fabiangeissler/robosax-ledbox/KiCad/output/render top 3d.jpg

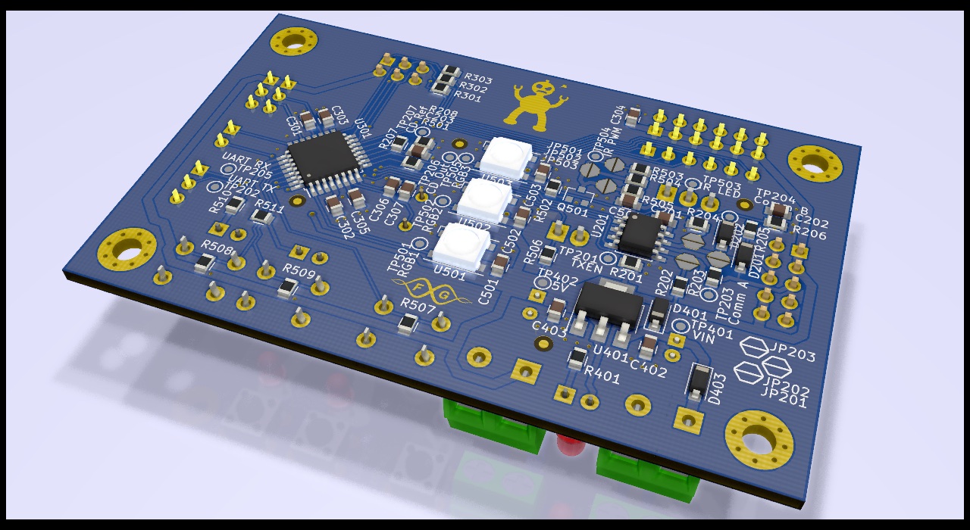
KiCad/output/render top 3d.jpg
