fabiangeissler/robosax-ledbox/Dokumentation/Fotos/IMG_1931.JPG

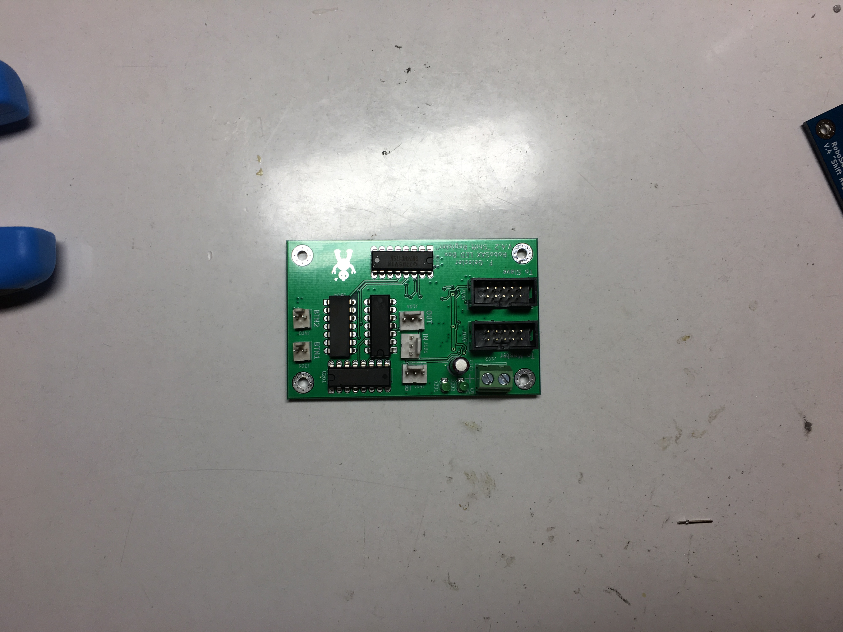
Dokumentation/Fotos/IMG_1931.JPG
