fabiangeissler/robosax-ledbox/Dokumentation/Fotos/IMG_1933.JPG

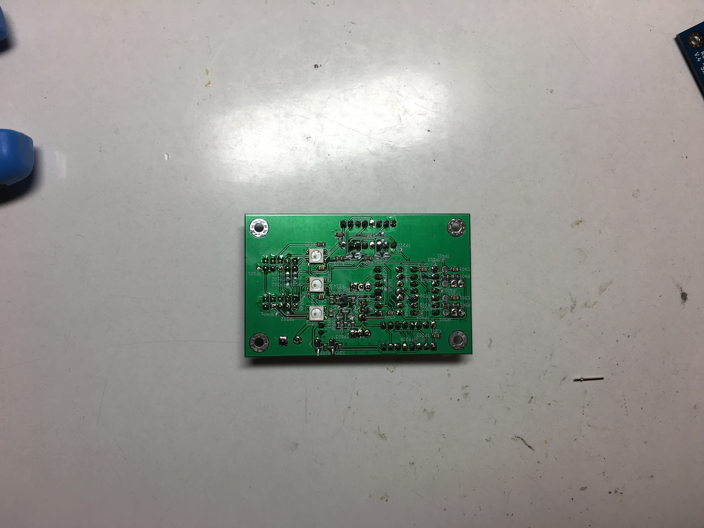
Dokumentation/Fotos/IMG_1933.JPG
