fabiangeissler/robosax-ledbox/Dokumentation/Fotos/IMG_1934.JPG

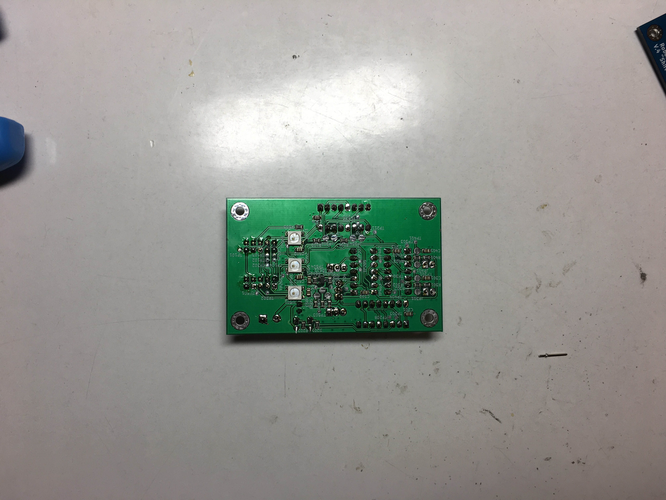
Dokumentation/Fotos/IMG_1934.JPG
