fabiangeissler/robosax-ledbox/Dokumentation/Fotos/IMG_1935.JPG

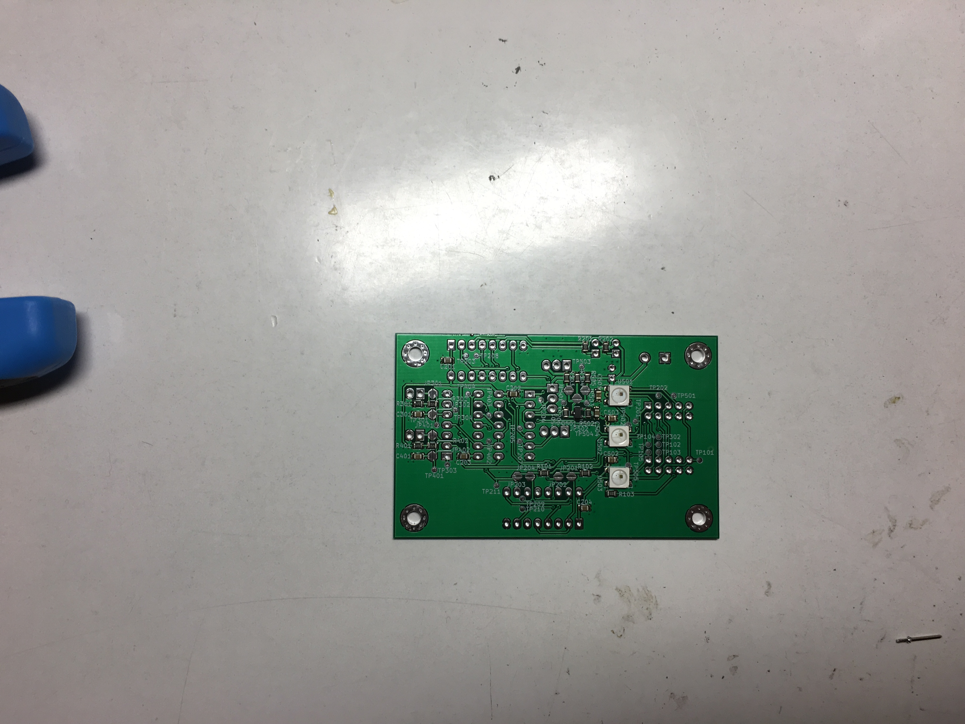
Dokumentation/Fotos/IMG_1935.JPG
