fabiangeissler/robosax-ledbox/KiCad/output/render bot 3d.jpg

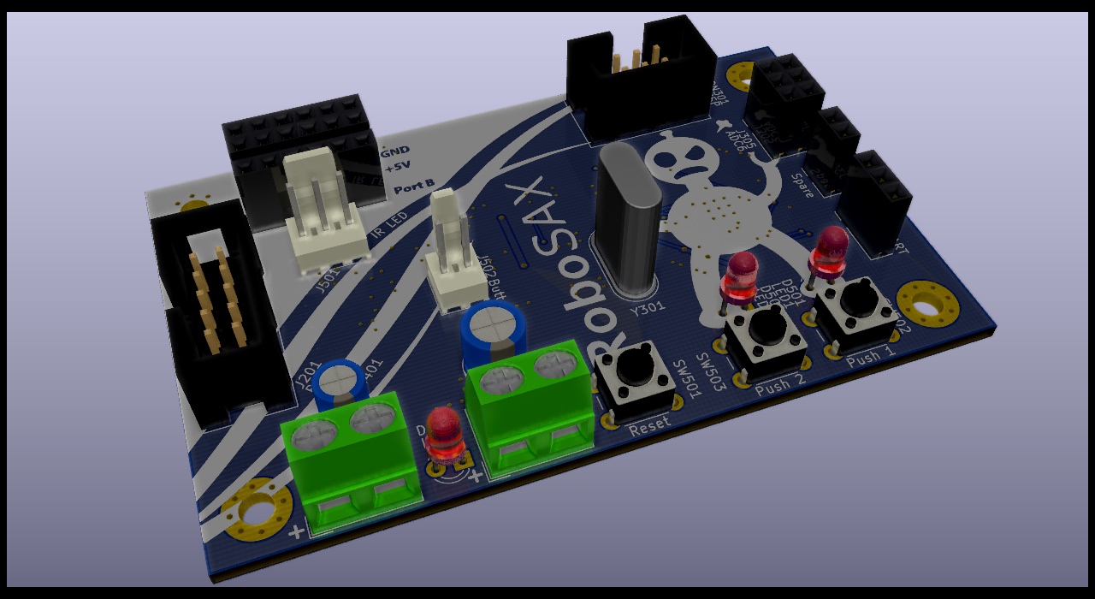
KiCad/output/render bot 3d.jpg
