fabiangeissler/robosax-ledbox/KiCad/output/render bot.jpg

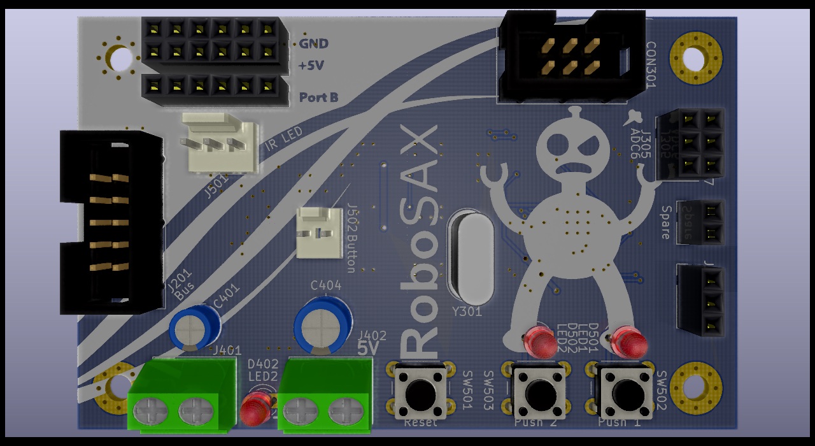
KiCad/output/render bot.jpg
