fabiangeissler/robosax-ledbox/KiCad/output/render top.jpg

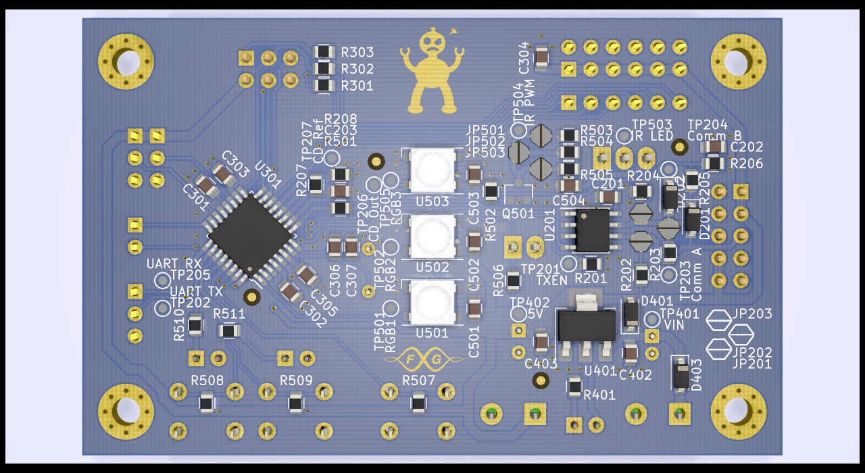
KiCad/output/render top.jpg
