fabiangeissler/robosax-ledbox/KiCad/output/ledbox.pdf

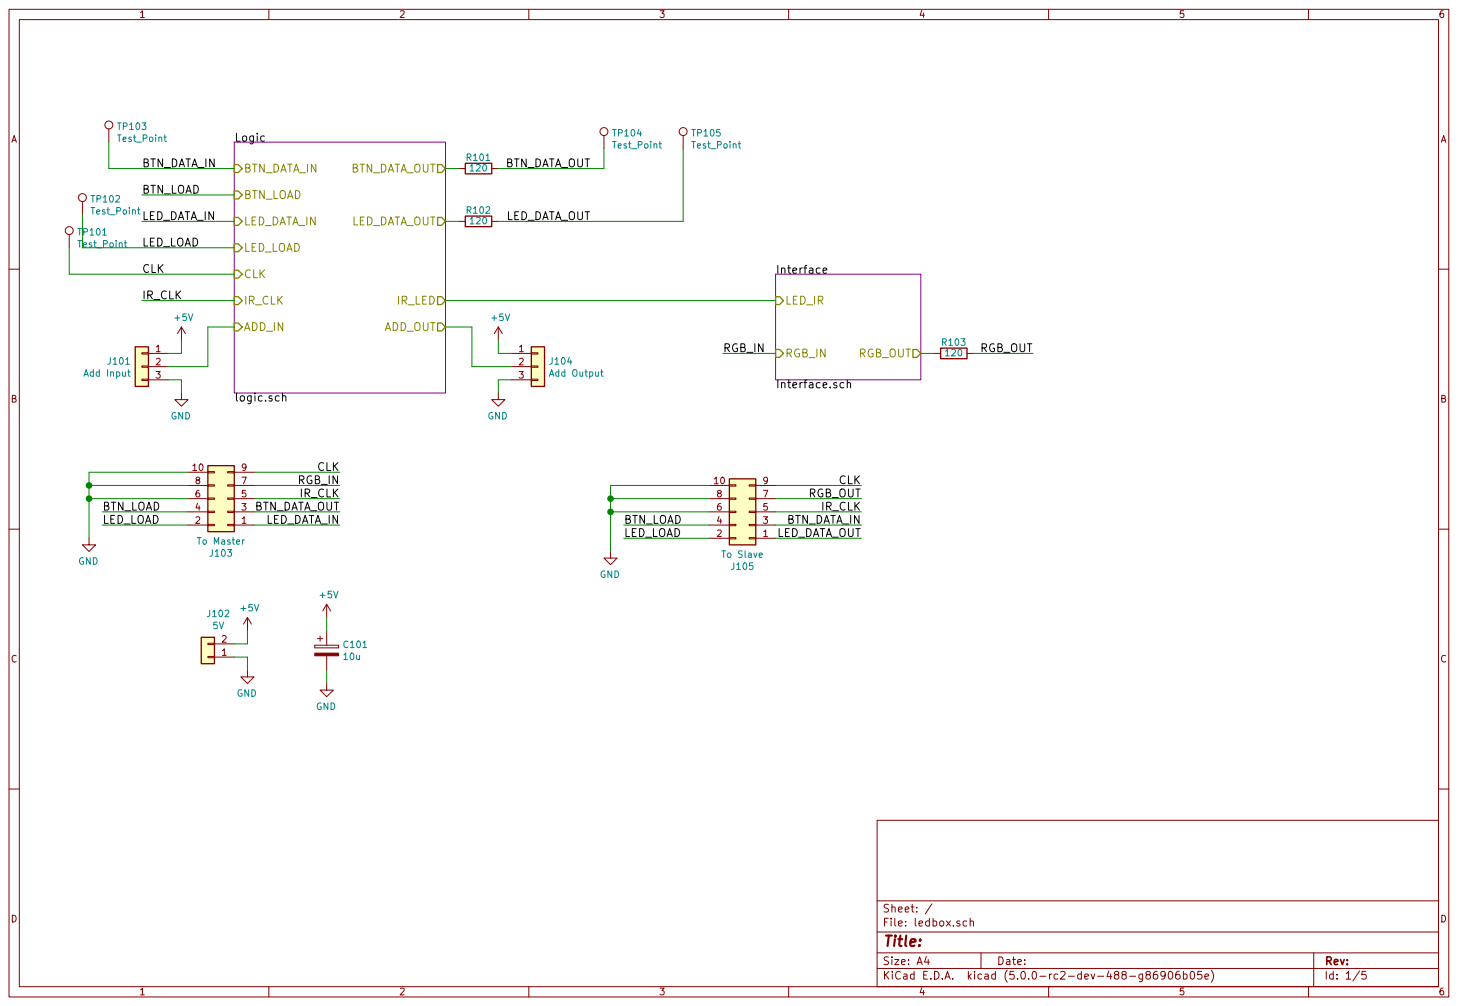
[picture p22: page 1]

Id: 1/5 Title: File: ledbox.sch Sheet: /

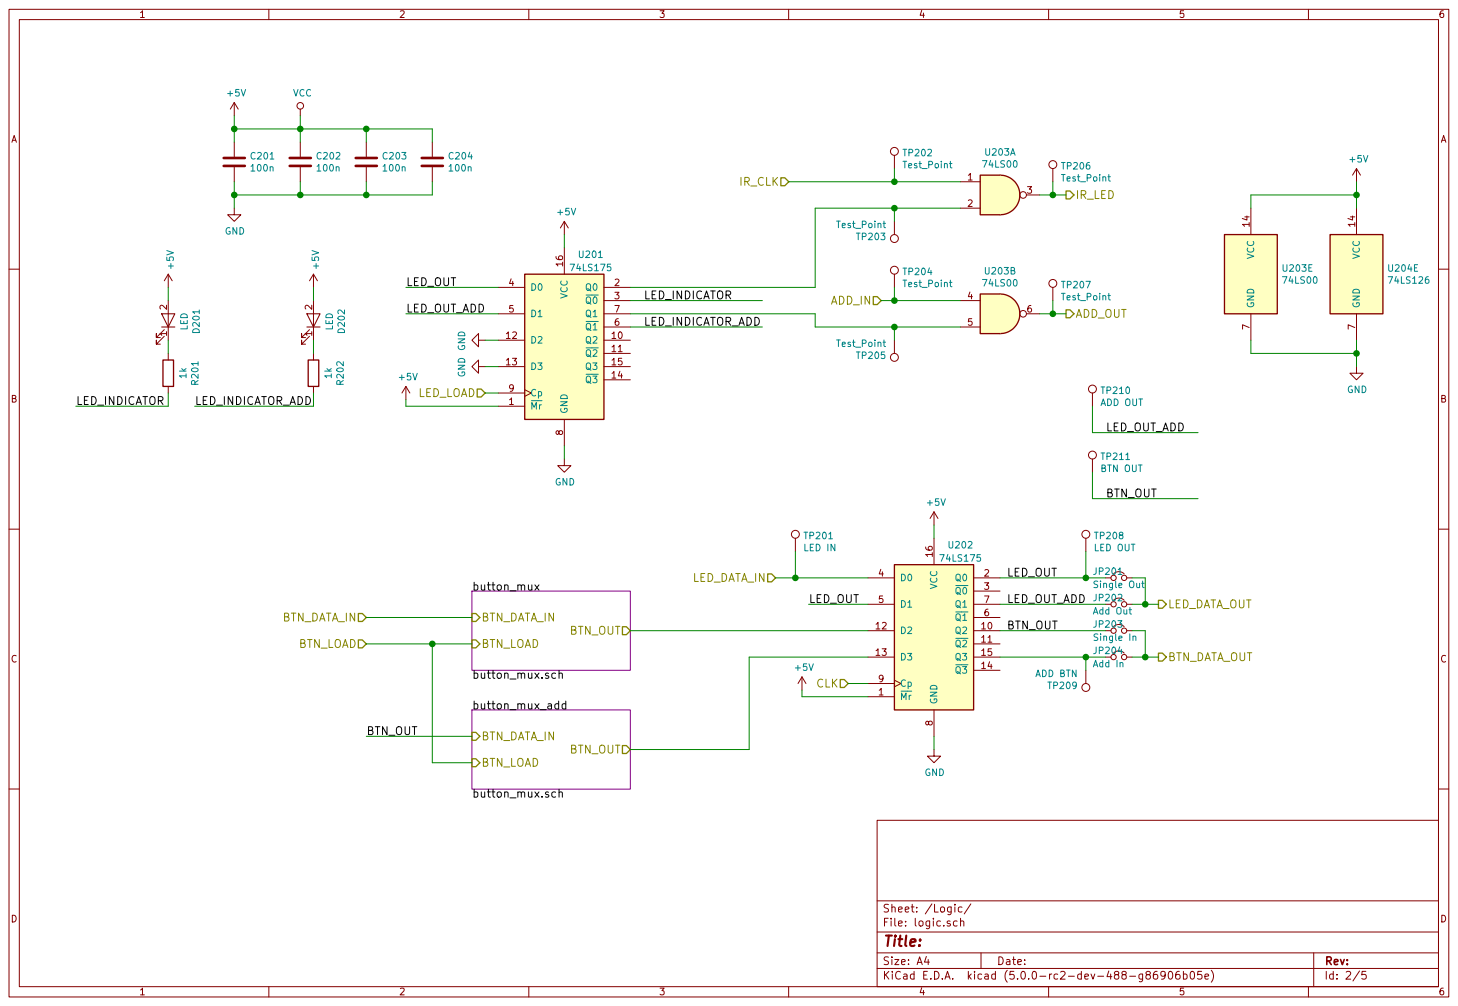
[picture p23: page 2]

JP201 Single Out JP202 Add Out LED_OUT

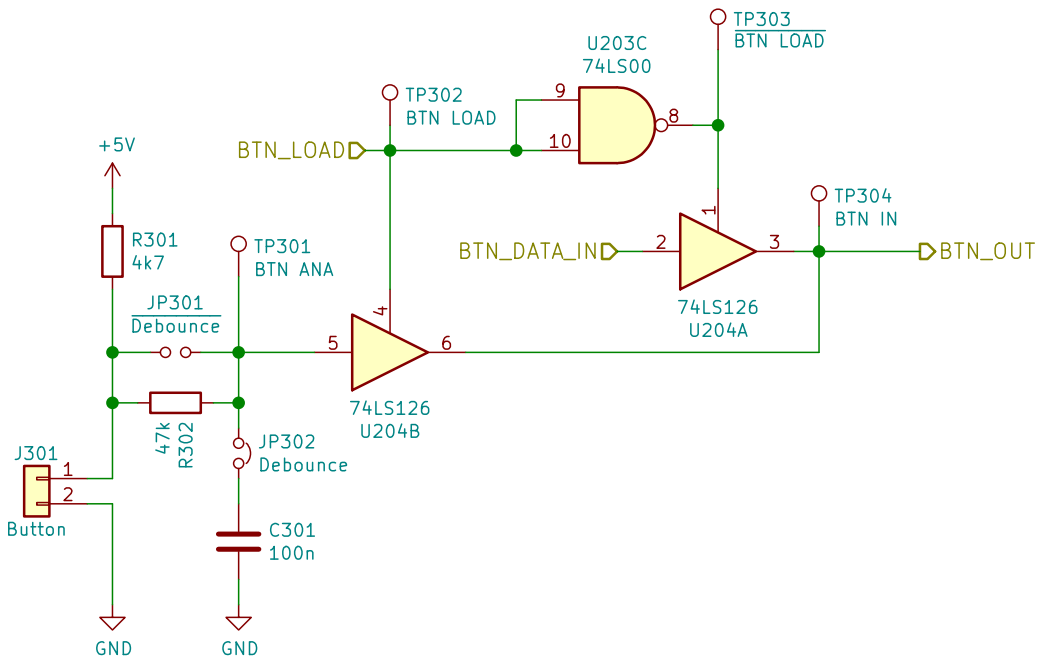
[picture p24: page 3]

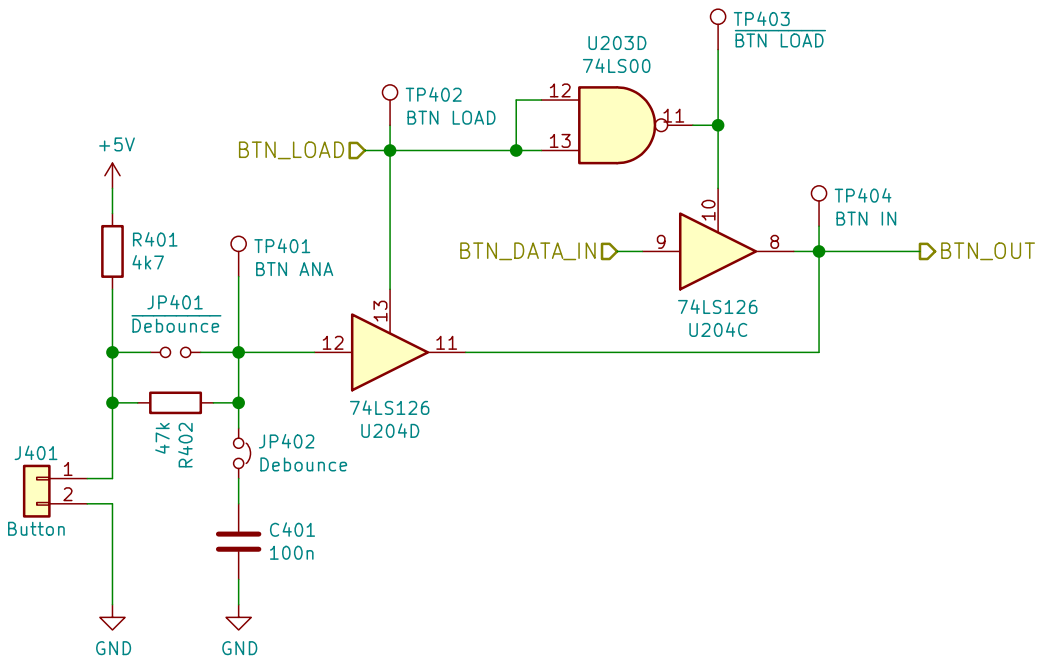
[picture p25: page 4]

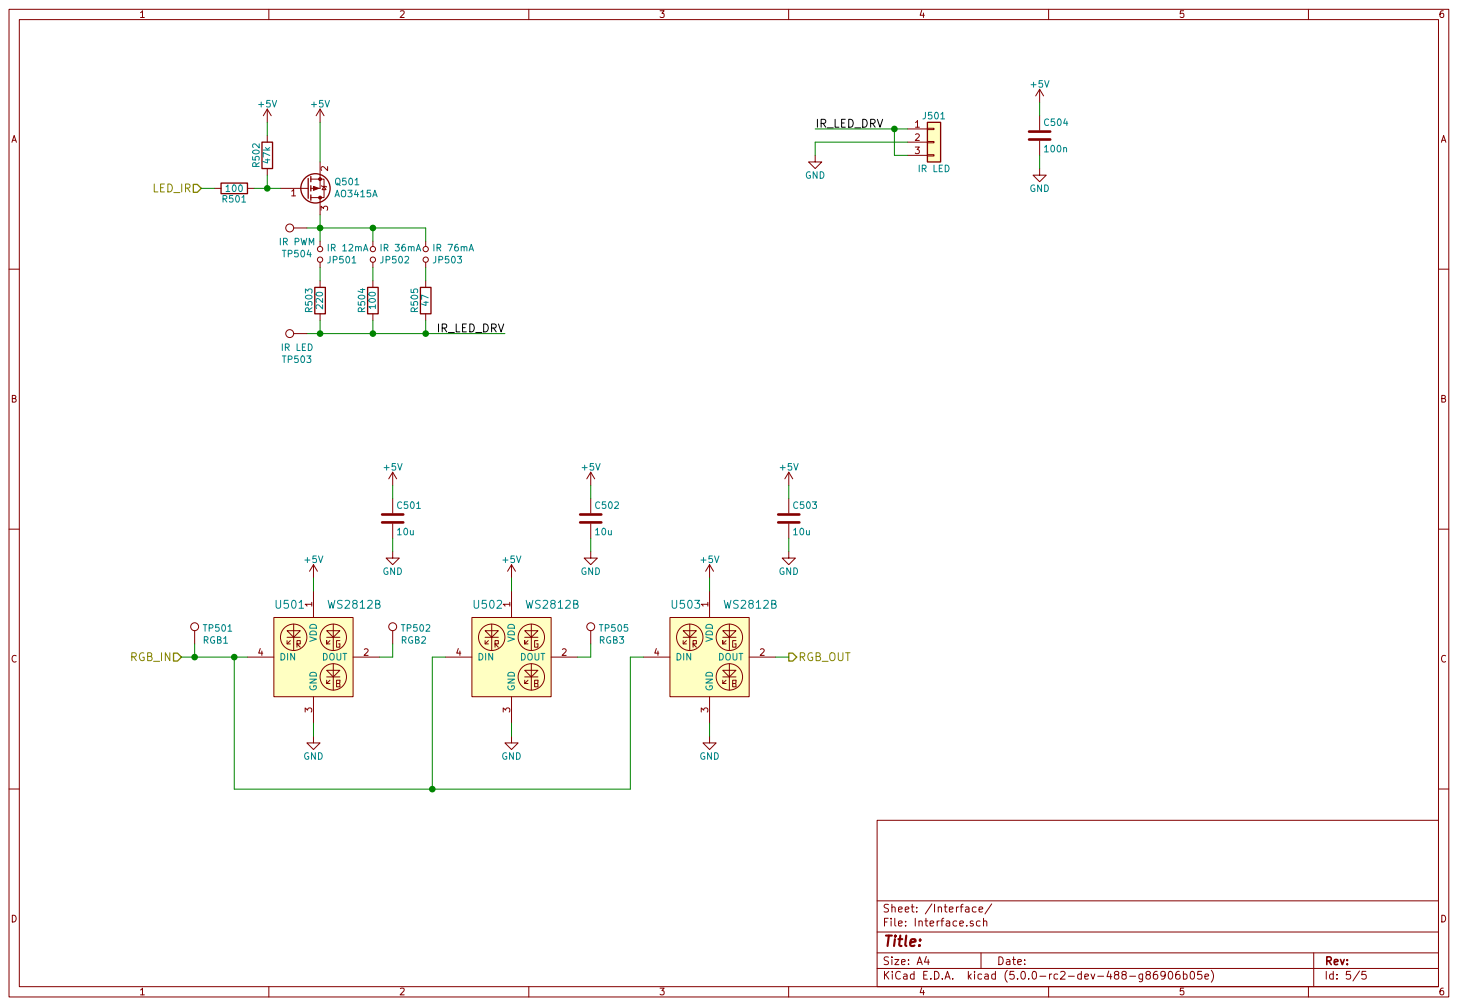
[picture p26: page 5]

Id: 5/5 Title: File: Interface.sch Sheet: /Interface/
