fabiangeissler/robosax-ledbox/KiCad/output/ledbox-B.Mask.pdf

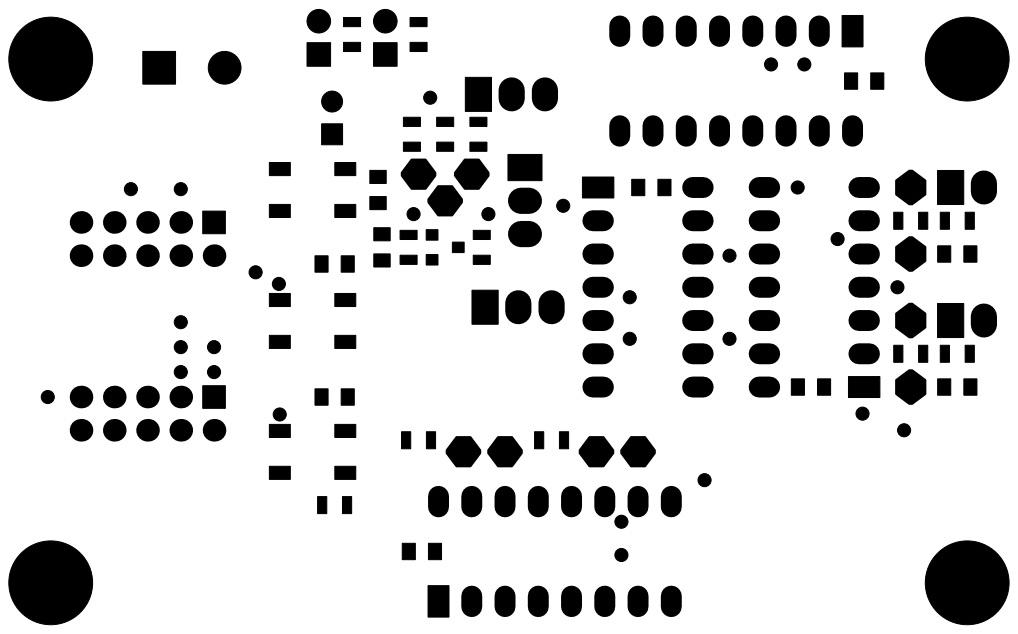
[picture p28: page 1]
