fabiangeissler/robosax-ledbox/KiCad/output/ledbox-B.SilkS.pdf

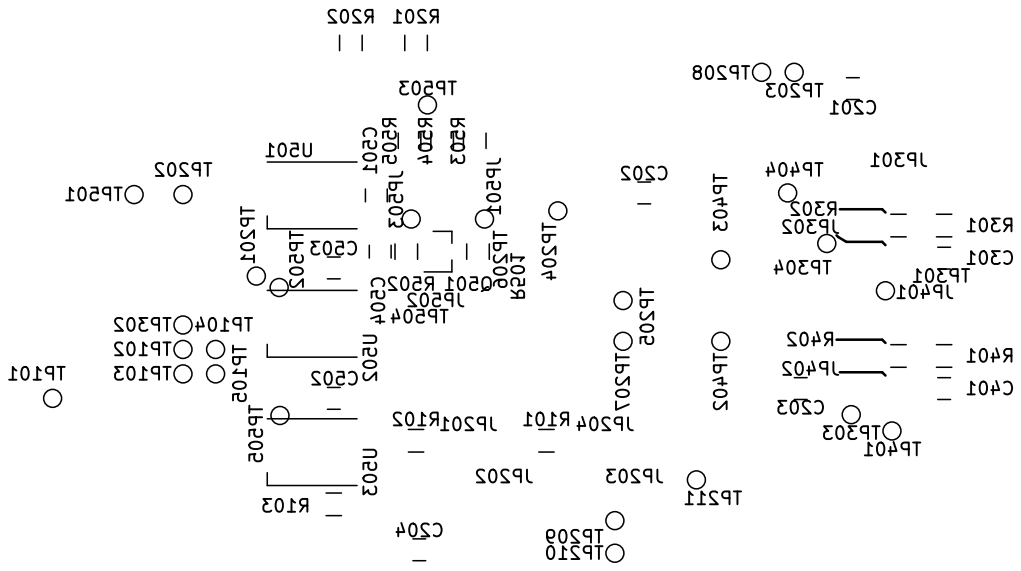
[picture p29: page 1]
