fabiangeissler/robosax-ledbox/KiCad/output/ledbox-F.Cu.pdf

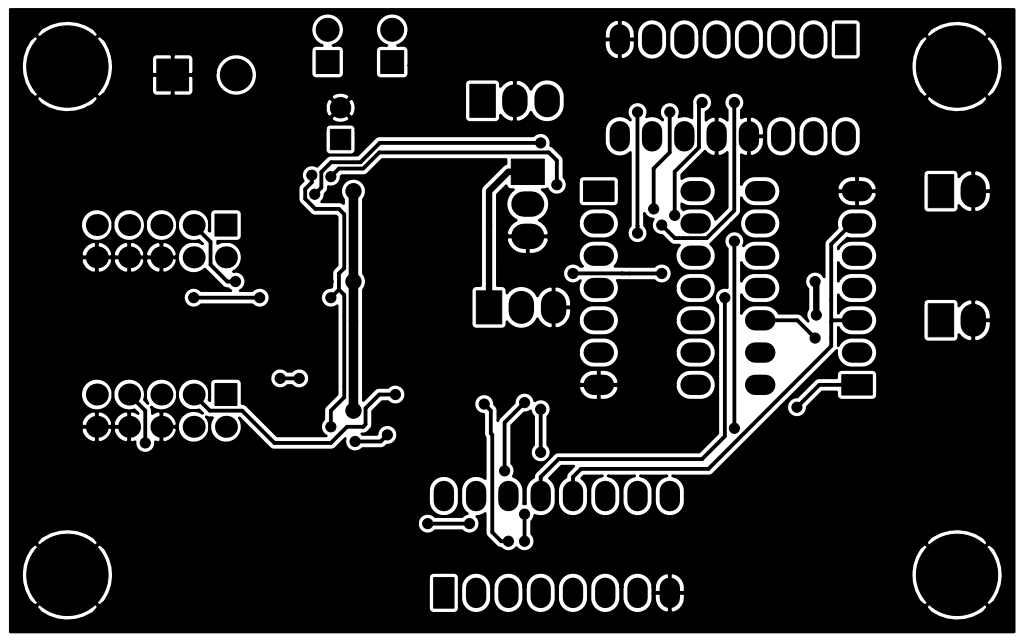
[picture p30: page 1]
