fabiangeissler/robosax-ledbox/KiCad/output/ledbox-F.Fab.pdf

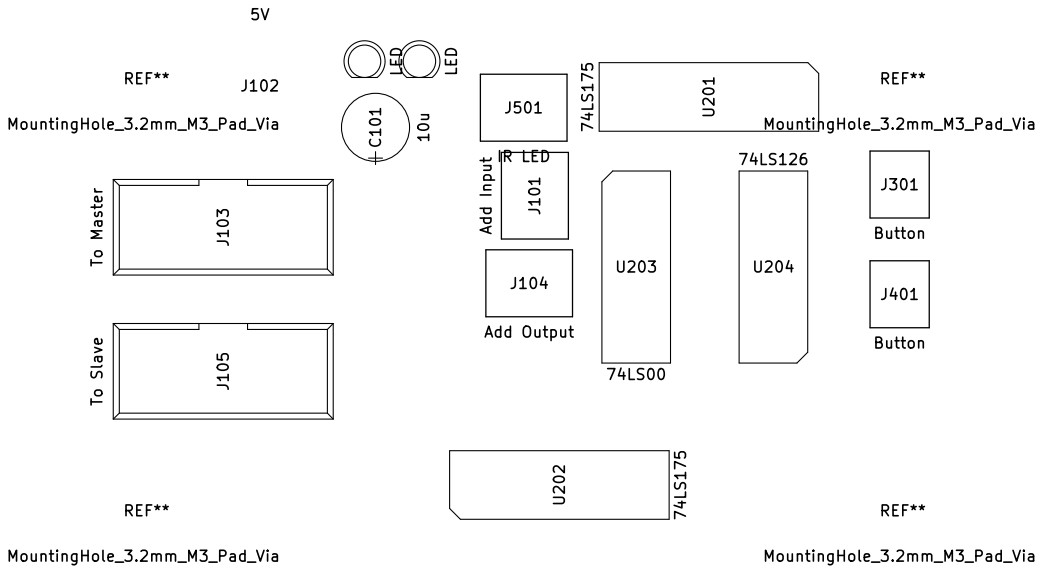
[picture p31: page 1]
