fabiangeissler/robosax-ledbox/KiCad/output/ledbox-F.Mask.pdf

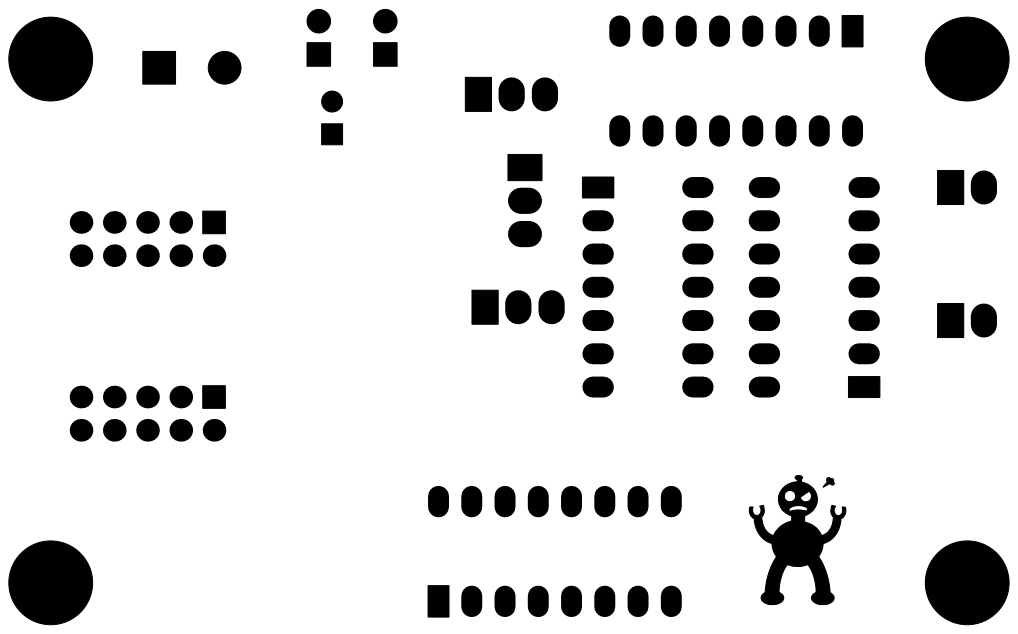
[picture p32: page 1]
