fabiangeissler/robosax-ledbox/KiCad/output/ledbox-F.SilkS.pdf

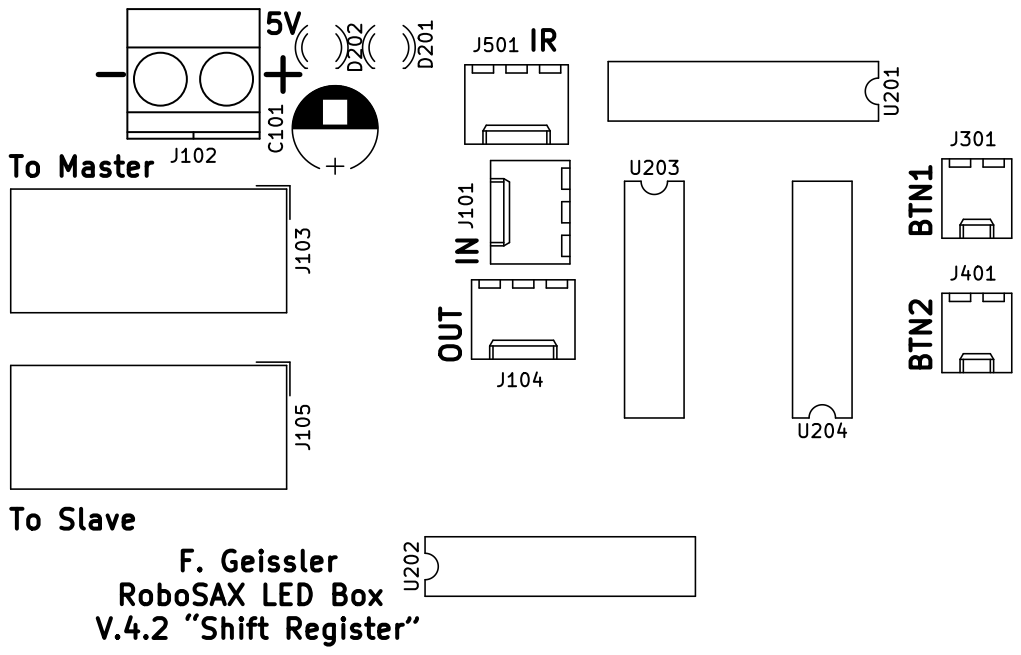
[picture p33: page 1]
