fabiangeissler/robosax-ledbox/Spice/Bus Kollision Sim.asc

C1: cap; 47p
C2: cap; 470p
D1: diode; 1N4148
D2: diode; 1N4148
R1: res; 100
R2: res; 22k
R3: res; 3k3
R4: res; 2k2
R5: res; 100k
R6: res; 100k
V1: voltage; PULSE(1 3.5 0 30n 30n 1u 2u); Rser=10
V2: voltage; PULSE(3.5 1 0 30n 30n 1u 2u); Rser=10
V3: voltage; PULSE(3.5 1 2.1u 30n 30n 1u 2u); Rser=10
V4: voltage; PULSE(1 3.5 2.1u 30n 30n 1u 2u); Rser=10
V5: voltage; 5
Named nets: 0, AIN0, AIN1, COMM_A, COMM_B
.tran 0 5u 0
